CASA0021/picnic-basket/e-paper/data/cloudy.bmp

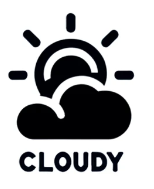
e-paper/data/cloudy.bmp
