CASA0021/picnic-basket/e-paper/data/rainy.bmp

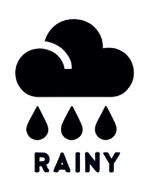
e-paper/data/rainy.bmp
