CASA0021/picnic-basket/e-paper/data/sunny.bmp

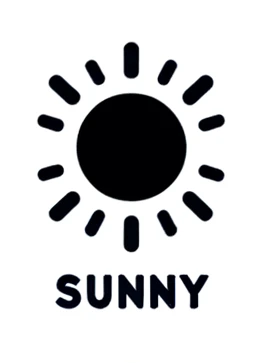
e-paper/data/sunny.bmp
