CASA0021/picnic-basket/GPP/ImageData.h

/*****************************************************************************
* | File      	:   ImageData.h
* | Author      :   Waveshare team
* | Function    :	
*----------------
* |	This version:   V1.0
* | Date        :   2018-10-23
* | Info        :
*
#
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

******************************************************************************/

#ifndef _IMAGEDATA_H_
#define _IMAGEDATA_H_
extern const unsigned char sun1[];
extern const unsigned char casa[];
extern const unsigned char uv[];
extern const unsigned char uv2[];
extern const unsigned char sun[];
extern const unsigned char green[];
extern const unsigned char medicine[];
extern const unsigned char mushroom[];
#endif
/* FILE END */
